411568/Atmega8_FM_radio/atmega8_code/work_in_progress/i2c.c

#include "i2c.h"

void initI2C(void) {
  TWBR = 32;                                 /* ustalenie szybkości transmisji */
                                             /* 8MHz / (16+2*TWBR*1) ~= 400/100kHz   2/32 */
  TWCR |= (1 << TWEN);                                            /* włączenie */
}

void i2cWaitForComplete(void) {
  loop_until_bit_is_set(TWCR, TWINT);
}

void i2cStart(void) {
  TWCR = (_BV(TWINT) | _BV(TWEN) | _BV(TWSTA));
  i2cWaitForComplete();
}

void i2cStop(void) {
  TWCR = (_BV(TWINT) | _BV(TWEN) | _BV(TWSTO));
}

uint8_t i2cReadAck(void) {
  TWCR = (_BV(TWINT) | _BV(TWEN) | _BV(TWEA));
  i2cWaitForComplete();
  return (TWDR);
}

uint8_t i2cReadNoAck(void) {
  TWCR = (_BV(TWINT) | _BV(TWEN));
  i2cWaitForComplete();
  return (TWDR);
}

void i2cSend(uint8_t data) {
  TWDR = data;
  TWCR = (_BV(TWINT) | _BV(TWEN));                    /* inicjacja i włączenie */
  i2cWaitForComplete();
}
